d3vv3/open-motorcycle-intercom/components/audio/audio_playout.c

/**
 * @file audio_playout.c
 * @brief Playout task: decode, adaptive render, mixing, I2S writes, heartbeat.
 */

#include <string.h>
#include <inttypes.h>

#include "esp_log.h"
#include "esp_timer.h"

#include "audio_internal.h"
#include "cpu_profile.h"

static const char *TAG = "audio";
static uint32_t successful_remote_decodes;

typedef struct {
    uint32_t attempted;
    uint32_t successful;
    uint32_t failed;
    uint32_t nonzero_frames;
    int32_t peak_abs;
} audio_output_window_t;

#if defined(AUDIO_S31_LC3_SELFTEST)
static bool run_lc3_startup_selftest(void)
{
    static int16_t zero_pcm[AUDIO_FRAME_SAMPLES] = {0};
    static int16_t patterned_pcm[AUDIO_FRAME_SAMPLES];
    static uint8_t packet[48];
    static int16_t decoded[AUDIO_FRAME_SAMPLES];

    for (size_t i = 0; i < AUDIO_FRAME_SAMPLES; ++i) {
        patterned_pcm[i] = ((i / 8u) & 1u) != 0u ? -10000 : 10000;
    }
    const int16_t *tests[] = {zero_pcm, patterned_pcm};
    const char *names[] = {"zero", "patterned"};
    for (size_t test = 0; test < 2u; ++test) {
        ESP_LOGI(TAG, "LC3 self-test %s encode/decode start", names[test]);
        int64_t encode_start = esp_timer_get_time();
        int encoded_bytes = esp_lc3_codec_encode20(g_audio.lc3_encoder, tests[test], packet);
        int64_t encode_us = esp_timer_get_time() - encode_start;
        int output_samples = -1;
        int64_t decode_us = 0;
        if (encoded_bytes == (int)sizeof(packet)) {
            int64_t decode_start = esp_timer_get_time();
            output_samples = esp_lc3_codec_decode20(g_audio.rx_sources[0].lc3_decoder,
                                                    packet, false, decoded);
            decode_us = esp_timer_get_time() - decode_start;
        }
        int32_t peak = 0;
        if (output_samples == AUDIO_FRAME_SAMPLES) {
            for (size_t i = 0; i < AUDIO_FRAME_SAMPLES; ++i) {
                int32_t sample = decoded[i];
                int32_t magnitude = sample < 0 ? -sample : sample;
                if (magnitude > peak) peak = magnitude;
            }
        }
        ESP_LOGI(TAG, "LC3 self-test %s encode/decode done: samples=%d bytes=%d"
                      " encode_us=%" PRId64 " decode_us=%" PRId64 " peak=%" PRId32,
                 names[test], output_samples, encoded_bytes, encode_us, decode_us, peak);
        if (encoded_bytes != (int)sizeof(packet) || output_samples != AUDIO_FRAME_SAMPLES ||
            (test == 1u && peak == 0)) {
            ESP_LOGE(TAG, "LC3 self-test %s failed", names[test]);
            return false;
        }
    }

    /* Captured 48B peer diagnostic samples only; these are never transmitted. */
    static const uint8_t peer_packets[][48] = {
        {
            0x06, 0x00, 0x1a, 0x9e, 0x0c, 0x0e, 0xfa, 0xe3,
            0x6a, 0xb3, 0x2d, 0x83, 0x65, 0xf7, 0xe9, 0xfe,
            0x0e, 0x2e, 0x7b, 0xe5, 0x33, 0x51, 0x10, 0x79,
            0x00, 0x00, 0x10, 0x33, 0x22, 0x29, 0x21, 0xad,
            0xf1, 0x84, 0x20, 0x9a, 0xe1, 0xc5, 0x56, 0xba,
            0x4f, 0xd9, 0xd3, 0x59, 0x33, 0x53, 0x1e, 0x37,
        },
        {
            0x2c, 0xbc, 0x25, 0x88, 0x90, 0x21, 0x67, 0xe3,
            0xf0, 0xed, 0xd6, 0x35, 0xad, 0xc8, 0x68, 0x4f,
            0x0e, 0x66, 0x2a, 0xeb, 0x33, 0x51, 0x1a, 0x65,
            0x00, 0x00, 0x16, 0x77, 0xa5, 0xbe, 0xcd, 0x15,
            0x9e, 0xf7, 0x8d, 0x6c, 0xfd, 0x7b, 0x57, 0xfe,
            0xa8, 0x67, 0x21, 0xaa, 0x8b, 0x57, 0x26, 0x4b,
        },
    };
    const char *peer_names[] = {"peer-old", "peer-new"};
    for (size_t test = 0; test < 2u; ++test) {
        int reset = esp_lc3_codec_reset(g_audio.rx_sources[0].lc3_decoder);
        if (reset != 0) {
            ESP_LOGE(TAG, "LC3 self-test %s decoder reset failed: %d", peer_names[test], reset);
            return false;
        }
        ESP_LOGI(TAG, "LC3 self-test %s decode start", peer_names[test]);
        int64_t decode_start = esp_timer_get_time();
        int output_samples = esp_lc3_codec_decode20(g_audio.rx_sources[0].lc3_decoder,
                                                    peer_packets[test], false, decoded);
        int64_t decode_us = esp_timer_get_time() - decode_start;
        int32_t peak = 0;
        if (output_samples == AUDIO_FRAME_SAMPLES) {
            for (size_t i = 0; i < AUDIO_FRAME_SAMPLES; ++i) {
                int32_t sample = decoded[i];
                int32_t magnitude = sample < 0 ? -sample : sample;
                if (magnitude > peak) peak = magnitude;
            }
        }
        ESP_LOGI(TAG, "LC3 self-test %s decode done: samples=%d decode_us=%" PRId64
                      " peak=%" PRId32,
                 peer_names[test], output_samples, decode_us, peak);
        if (output_samples != AUDIO_FRAME_SAMPLES) {
            ESP_LOGE(TAG, "LC3 self-test %s failed", peer_names[test]);
            return false;
        }
    }

    int decoder_reset = esp_lc3_codec_reset(g_audio.rx_sources[0].lc3_decoder);
    int encoder_reset = esp_lc3_codec_reset(g_audio.lc3_encoder);
    if (decoder_reset != 0 || encoder_reset != 0) {
        ESP_LOGE(TAG, "LC3 self-test reset failed: decoder=%d encoder=%d",
                 decoder_reset, encoder_reset);
        return false;
    }
    ESP_LOGI(TAG, "LC3 startup self-tests passed; encoder and decoder reset");
    return true;
}
#endif

static void add_timing_us(uint64_t *sum, uint64_t value)
{
    *sum = UINT64_MAX - *sum < value ? UINT64_MAX : *sum + value;
}

static void record_timing(uint32_t *count, uint64_t *sum, uint32_t *maximum, uint32_t us)
{
    if (*count != UINT32_MAX) (*count)++;
    add_timing_us(sum, us);
    if (us > *maximum) *maximum = us;
}

typedef struct {
    audio_packet_store_pop_result_t result;
    audio_packet_t packet;
} audio_playout_event_t;

void audio_playout_reset_far_reference(void)
{
    portENTER_CRITICAL(&g_audio_far_ref_lock);
    memset(g_audio.far_ref_frame, 0, sizeof(g_audio.far_ref_frame));
    memset(g_audio.far_ref_shadows, 0, sizeof(g_audio.far_ref_shadows));
    g_audio.far_ref_shadow_head = 0u;
    portEXIT_CRITICAL(&g_audio_far_ref_lock);
}

/*
 * Each shadow follows one preloaded/submitted DMA descriptor. A successful
 * blocking write means the oldest descriptor completed and can become the AEC
 * reference; the new final mix takes its place in that descriptor's shadow.
 */
static void advance_far_reference_after_write(void)
{
#if AUDIO_ENABLE_AEC_NS && AUDIO_ENABLE_ESP_SR_AEC
    /* No reference conversion is needed when AEC is compiled out. */
    for (size_t offset = 0u; offset < AUDIO_HW_FRAME_SAMPLES;
         offset += AUDIO_RATE_CONVERTER_MAX_INPUT_FRAMES) {
        size_t converted = 0u;
        if (audio_rate_converter_process(g_audio.far_reference_converter,
                                         &g_audio.hw_output[offset],
                                         AUDIO_RATE_CONVERTER_MAX_INPUT_FRAMES,
                                         g_audio.far_converted, AUDIO_FRAME_SAMPLES,
                                         &converted) != 0 ||
            audio_sample_fifo_write(&g_audio.far_fifo, g_audio.far_converted, converted) != converted) {
            audio_playout_reset_far_reference();
            (void)audio_rate_converter_reset(g_audio.far_reference_converter);
            audio_sample_fifo_reset(&g_audio.far_fifo);
            return;
        }
    }
    memset(g_audio.far_pending_frame, 0, AUDIO_FRAME_SAMPLES * sizeof(int16_t));
    (void)audio_sample_fifo_read(&g_audio.far_fifo, g_audio.far_pending_frame,
                                 AUDIO_FRAME_SAMPLES);
    portENTER_CRITICAL(&g_audio_far_ref_lock);
    memcpy(g_audio.far_converted, g_audio.far_pending_frame,
           AUDIO_FRAME_SAMPLES * sizeof(int16_t));
    memcpy(g_audio.far_ref_frame, g_audio.far_ref_shadows[g_audio.far_ref_shadow_head],
           sizeof(g_audio.far_ref_frame));
    memcpy(g_audio.far_ref_shadows[g_audio.far_ref_shadow_head], g_audio.far_converted,
           sizeof(g_audio.far_ref_shadows[g_audio.far_ref_shadow_head]));
    g_audio.far_ref_shadow_head = (g_audio.far_ref_shadow_head + 1u) % I2S_DMA_BUFFER_COUNT;
    portEXIT_CRITICAL(&g_audio_far_ref_lock);
#endif
}

static void record_decode_result(int samples, int64_t decode_time_us, int64_t *decode_time_sum)
{
    if (samples != AUDIO_FRAME_SAMPLES) {
        AUDIO_STATS_LOCK();
        g_audio.stats.decode_errors++;
        AUDIO_STATS_UNLOCK();
        ESP_LOGW(TAG, "Opus decode failed: %d", samples);
        return;
    }
    if (decode_time_us > 0) {
        uint64_t sum = *decode_time_sum > 0 ? (uint64_t)*decode_time_sum : 0u;
        sum = UINT64_MAX - sum < (uint64_t)decode_time_us
            ? UINT64_MAX : sum + (uint64_t)decode_time_us;
        *decode_time_sum = sum > INT64_MAX ? INT64_MAX : (int64_t)sum;
    }
    AUDIO_STATS_LOCK();
    if (g_audio.stats.frames_decoded != UINT32_MAX) g_audio.stats.frames_decoded++;
    if (g_audio.stats.frames_decoded != 0u) {
        g_audio.stats.decode_time_us_avg = (uint32_t)(
            (uint64_t)*decode_time_sum / g_audio.stats.frames_decoded);
    }
    if ((uint32_t)decode_time_us > g_audio.stats.decode_time_us_max) {
        g_audio.stats.decode_time_us_max = (uint32_t)decode_time_us;
    }
    AUDIO_STATS_UNLOCK();
}

static void update_depth_stats(uint16_t packet_depth)
{
    uint8_t depth = packet_depth > UINT8_MAX ? UINT8_MAX : (uint8_t)packet_depth;
    AUDIO_STATS_LOCK();
    g_audio.stats.jitter_buffer_depth = depth;
    if (g_audio.stats.playout_task_loops == 1 || depth < g_audio.stats.rx_q_depth_min) {
        g_audio.stats.rx_q_depth_min = depth;
    }
    if (depth > g_audio.stats.rx_q_depth_max) {
        g_audio.stats.rx_q_depth_max = depth;
    }
    uint64_t previous =
        (uint64_t)g_audio.stats.rx_q_depth_avg * (uint64_t)(g_audio.stats.playout_task_loops - 1u);
    g_audio.stats.rx_q_depth_avg = (uint8_t)((previous + depth) / g_audio.stats.playout_task_loops);
    AUDIO_STATS_UNLOCK();
}

static void record_rx_pipe_latency(const audio_packet_t *packet, int64_t decode_start)
{
    if (packet->received_us == 0u || (uint64_t)decode_start < packet->received_us) {
        return;
    }
    uint64_t rx_pipe_us = (uint64_t)decode_start - packet->received_us;
    AUDIO_STATS_LOCK();
    if (g_audio.rx_pipe_count != UINT32_MAX) g_audio.rx_pipe_count++;
    add_timing_us(&g_audio.rx_pipe_sum_us, rx_pipe_us);
    if (g_audio.rx_pipe_count != 0u) {
        g_audio.stats.rx_pipe_us_avg = (uint32_t)(g_audio.rx_pipe_sum_us / g_audio.rx_pipe_count);
    }
    if (rx_pipe_us > g_audio.stats.rx_pipe_us_max) {
        g_audio.stats.rx_pipe_us_max = rx_pipe_us > UINT32_MAX ? UINT32_MAX : (uint32_t)rx_pipe_us;
    }
    AUDIO_STATS_UNLOCK();
}

/* Unassigns the source after 1 s without packets; reports whether decode may run. */
static bool refresh_source_assignment(audio_rx_source_t *source, uint64_t now_ms)
{
    bool assigned;
    bool reset_decoder = false;
    bool was_pending = false;

    xSemaphoreTake(g_audio.rx_sources_mutex, portMAX_DELAY);
    assigned = source->assigned;
    if (source->decoder_reset_pending) {
        was_pending = true;
        source->decoder_reset_pending = false;
        reset_decoder = true;
    }
    if (assigned && audio_packet_store_depth(&source->packet_store) == 0u &&
        now_ms - source->last_enqueue_ms >= RX_SOURCE_IDLE_TIMEOUT_MS) {
        source->assigned = false;
        source->source_id = 0;
        source->last_active_ms = 0;
        source->decoder_reset_pending = false;
        audio_packet_store_reset(&source->packet_store);
        assigned = false;
        reset_decoder = true;
    }
    xSemaphoreGive(g_audio.rx_sources_mutex);

    if (reset_decoder) {
        bool reset_ok = true;
#if defined(AUDIO_S31_LC3_WIRE)
        if (g_audio.config.mode == AUDIO_MODE_MESH) {
            reset_ok = esp_lc3_codec_reset(source->lc3_decoder) == 0;
        } else
#endif
        {
            opus_decoder_ctl(source->decoder, OPUS_RESET_STATE);
        }
        audio_pcm_resampler_reset(&source->resampler);
        source->decoded_active = false;
        if (!reset_ok && was_pending) {
            xSemaphoreTake(g_audio.rx_sources_mutex, portMAX_DELAY);
            if (source->assigned) source->decoder_reset_pending = true;
            xSemaphoreGive(g_audio.rx_sources_mutex);
            return false;
        }
    }
    return assigned;
}

/* Pops due packets while resampler room allows; returns false when unassigned. */
static bool pop_due_events(audio_rx_source_t *source, uint64_t now_ms,
                           audio_playout_event_t *events, size_t *event_count,
                           uint16_t *packet_depth, size_t *upstream_samples)
{
    size_t event_limit = audio_pcm_resampler_admission_blocks(&source->resampler);
    if (event_limit > AUDIO_PACKET_STORE_CAPACITY) {
        event_limit = AUDIO_PACKET_STORE_CAPACITY;
    }

    bool assigned = true;
    *event_count = 0;
    xSemaphoreTake(g_audio.rx_sources_mutex, portMAX_DELAY);
    if (source->assigned) {
        size_t count;
        uint32_t popped = 0u;
        for (count = 0; count < event_limit; ++count) {
            audio_playout_event_t *event = &events[count];
            event->result = audio_packet_store_pop(&source->packet_store, now_ms, &event->packet);
            if (event->result == AUDIO_PACKET_STORE_POP_NOT_DUE) {
                break;
            }
            if (event->result == AUDIO_PACKET_STORE_POP_PACKET) {
                popped++;
            }
        }
        if (popped != 0u) {
            AUDIO_STATS_LOCK();
            g_audio.stats.rx_store_pop += popped;
            AUDIO_STATS_UNLOCK();
        }
        *event_count = count;
        size_t remaining_depth = audio_packet_store_depth(&source->packet_store);
        *packet_depth += (uint16_t)remaining_depth;
        *upstream_samples = remaining_depth * AUDIO_FRAME_SAMPLES;
    } else {
        assigned = false;
    }
    xSemaphoreGive(g_audio.rx_sources_mutex);
    return assigned;
}

static void decode_event_into_resampler(audio_rx_source_t *source, audio_playout_event_t *event,
                                        int64_t *decode_time_sum)
{
    bool packet_event = event->result == AUDIO_PACKET_STORE_POP_PACKET;
    if (packet_event) {
        source->decoded_active = event->packet.active;
    } else if (event->result == AUDIO_PACKET_STORE_POP_DTX_IDLE) {
        source->decoded_active = false;
    }

    int16_t decoded[AUDIO_FRAME_SAMPLES];
    int64_t decode_start = esp_timer_get_time();
#if defined(AUDIO_S31_LC3_WIRE)
    bool lc3_wire = g_audio.config.mode == AUDIO_MODE_MESH;
    int samples;
#if defined(AUDIO_S31_LC3_SKIP_RX)
    if (lc3_wire) {
        memset(decoded, 0, sizeof(decoded));
        samples = AUDIO_FRAME_SAMPLES;
    } else {
        samples = packet_event
                      ? opus_decode(source->decoder, event->packet.data,
                                    (opus_int32)event->packet.length, decoded,
                                    AUDIO_FRAME_SAMPLES, 0)
                      : opus_decode(source->decoder, NULL, 0, decoded,
                                    AUDIO_FRAME_SAMPLES, 0);
    }
#else
    samples = lc3_wire
                      ? esp_lc3_codec_decode20(source->lc3_decoder,
                                               packet_event ? event->packet.data : NULL,
                                               !packet_event, decoded)
                      : (packet_event
                             ? opus_decode(source->decoder, event->packet.data,
                                           (opus_int32)event->packet.length, decoded,
                                           AUDIO_FRAME_SAMPLES, 0)
                             : opus_decode(source->decoder, NULL, 0, decoded,
                                           AUDIO_FRAME_SAMPLES, 0));
#endif
#else
    int samples =
        packet_event
            ? opus_decode(source->decoder, event->packet.data, (opus_int32)event->packet.length,
                          decoded, AUDIO_FRAME_SAMPLES, 0)
            : opus_decode(source->decoder, NULL, 0, decoded, AUDIO_FRAME_SAMPLES, 0);
#endif
    int64_t decode_time = esp_timer_get_time() - decode_start;

    if (packet_event) {
        record_rx_pipe_latency(&event->packet, decode_start);
#if defined(AUDIO_S31_LC3_SKIP_RX)
        if (!lc3_wire) {
            record_decode_result(samples, decode_time, decode_time_sum);
        }
#else
        record_decode_result(samples, decode_time, decode_time_sum);
#endif
#if !defined(AUDIO_S31_LC3_SKIP_RX)
        if (samples == AUDIO_FRAME_SAMPLES && successful_remote_decodes < 100u) {
            successful_remote_decodes++;
            if (successful_remote_decodes == 1u || successful_remote_decodes == 100u) {
                ESP_LOGI(TAG, "Remote audio decode count=%" PRIu32
                         " playout stack high water: %u bytes",
                         successful_remote_decodes,
                         (unsigned)uxTaskGetStackHighWaterMark(NULL));
            }
        }
#endif
    } else if (samples != AUDIO_FRAME_SAMPLES) {
        AUDIO_STATS_LOCK();
        g_audio.stats.decode_errors++;
        AUDIO_STATS_UNLOCK();
        ESP_LOGW(TAG, "Audio PLC failed: %d", samples);
    } else if (event->result == AUDIO_PACKET_STORE_POP_MISSING) {
        AUDIO_STATS_LOCK();
        g_audio.stats.seq_gap_frames++;
        g_audio.stats.conceal_loss_frames++;
        AUDIO_STATS_UNLOCK();
    } else {
        AUDIO_STATS_LOCK();
        g_audio.stats.plc_frames++;
        AUDIO_STATS_UNLOCK();
    }

    if (samples == AUDIO_FRAME_SAMPLES) {
        audio_pcm_resampler_telemetry_t push = audio_pcm_resampler_push(
            &source->resampler, decoded, AUDIO_FRAME_SAMPLES, source->decoded_active);
        if (push.rejected_push) {
            AUDIO_STATS_LOCK();
            g_audio.stats.pcm_fifo_overflows++;
            g_audio.stats.frames_dropped++;
            g_audio.stats.glitches_detected++;
            AUDIO_STATS_UNLOCK();
        }
    }
}

static bool decode_and_buffer_source(audio_rx_source_t *source, uint64_t now_ms,
                                     int64_t *decode_time_sum, uint16_t *packet_depth,
                                     size_t *upstream_samples)
{
    if (!refresh_source_assignment(source, now_ms)) {
        return false;
    }
    audio_playout_event_t events[AUDIO_PACKET_STORE_CAPACITY];
    size_t event_count = 0;
    if (!pop_due_events(source, now_ms, events, &event_count, packet_depth, upstream_samples)) {
        return false;
    }
    for (size_t i = 0; i < event_count; ++i) {
        decode_event_into_resampler(source, &events[i], decode_time_sum);
    }
    return true;
}

static bool render_remote_sources(uint64_t now_ms, int64_t *decode_time_sum)
{
    uint8_t active_sources = 0;
    uint8_t mixed_sources = 0;
    uint16_t packet_depth = 0;
    int32_t current_ppm = 0;
    int32_t current_abs_ppm = 0;
    bool recovery_active = false;
    memset(g_audio.mix_frame, 0, sizeof(g_audio.mix_frame));

    for (size_t source_index = 0; source_index < AUDIO_MAX_RX_SOURCES; ++source_index) {
        audio_rx_source_t *source = &g_audio.rx_sources[source_index];
        size_t upstream_samples = 0u;
        bool assigned = decode_and_buffer_source(source, now_ms, decode_time_sum, &packet_depth,
                                                 &upstream_samples);
        if (!assigned) {
            continue;
        }
        int16_t rendered[AUDIO_FRAME_SAMPLES];
        bool was_started = source->resampler.started;
        audio_pcm_resampler_telemetry_t render =
            audio_pcm_resampler_render(&source->resampler, rendered, upstream_samples);
        recovery_active = recovery_active || render.recovery_active;
        if (render.underrun) {
            AUDIO_STATS_LOCK();
            g_audio.stats.pcm_underruns++;
            g_audio.stats.rx_queue_underruns++;
            g_audio.stats.glitches_detected++;
            AUDIO_STATS_UNLOCK();
        }
        int32_t abs_ppm =
            render.correction_ppm < 0 ? -render.correction_ppm : render.correction_ppm;
        if (abs_ppm > current_abs_ppm) {
            current_abs_ppm = abs_ppm;
            current_ppm = render.correction_ppm;
        }
        if (render.audible_active && (render.started || (was_started && render.underrun))) {
            active_sources++;
            for (size_t i = 0; i < AUDIO_FRAME_SAMPLES; ++i) {
                g_audio.mix_frame[i] += rendered[i];
            }
            mixed_sources++;
        }
    }

    AUDIO_STATS_LOCK();
    g_audio.stats.active_rx_sources = active_sources;
    g_audio.stats.asrc_correction_ppm = current_ppm;
    g_audio.stats.asrc_recovery_active = recovery_active;
    if ((uint32_t)current_abs_ppm > g_audio.stats.asrc_correction_abs_max_ppm) {
        g_audio.stats.asrc_correction_abs_max_ppm = (uint32_t)current_abs_ppm;
    }
    AUDIO_STATS_UNLOCK();
    update_depth_stats(packet_depth);

    if (mixed_sources == 0) {
        memset(g_audio.pcm_output, 0, sizeof(g_audio.pcm_output));
        return false;
    }
    for (size_t i = 0; i < AUDIO_FRAME_SAMPLES; ++i) {
        int32_t sample = g_audio.mix_frame[i];
        if (mixed_sources > 1) {
            sample /= mixed_sources;
        }
        if (sample > INT16_MAX) {
            sample = INT16_MAX;
        } else if (sample < INT16_MIN) {
            sample = INT16_MIN;
        }
        g_audio.pcm_output[i] = (int16_t)sample;
    }
    return true;
}
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
